conbart/ritterburg/01-Ritterburg-OpenSCAD.png

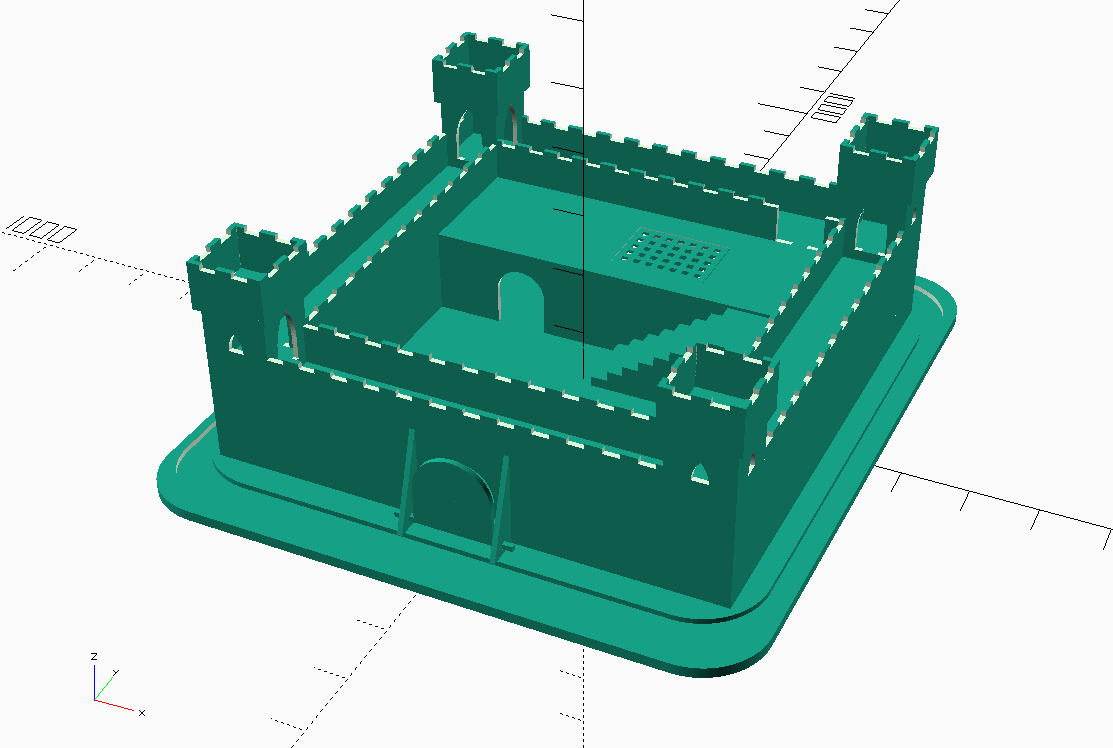
01-Ritterburg-OpenSCAD.png
