conbart/ritterburg/02-Lasercutter-Türme.jpg

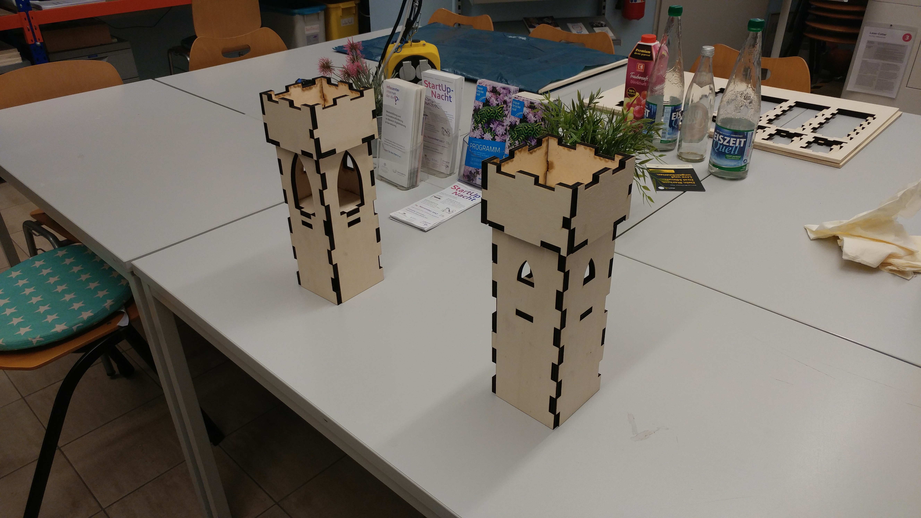
02-Lasercutter-Türme.jpg
