conbart/ritterburg/03-Lasercutter-Burg.jpg

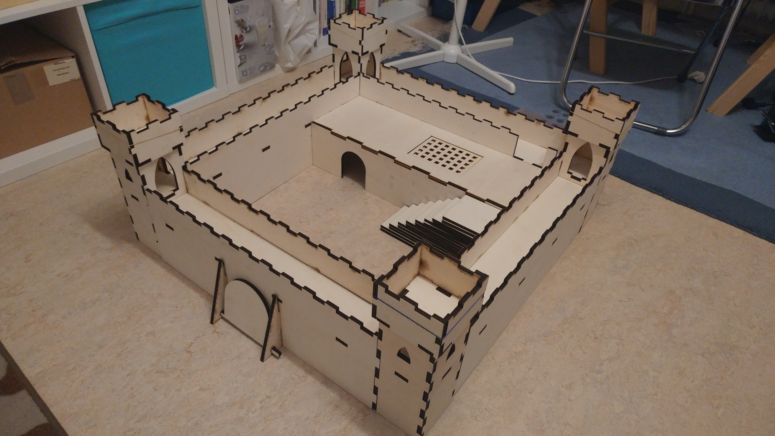
03-Lasercutter-Burg.jpg
