conbart/ritterburg/04-Dremel-Relief.jpg

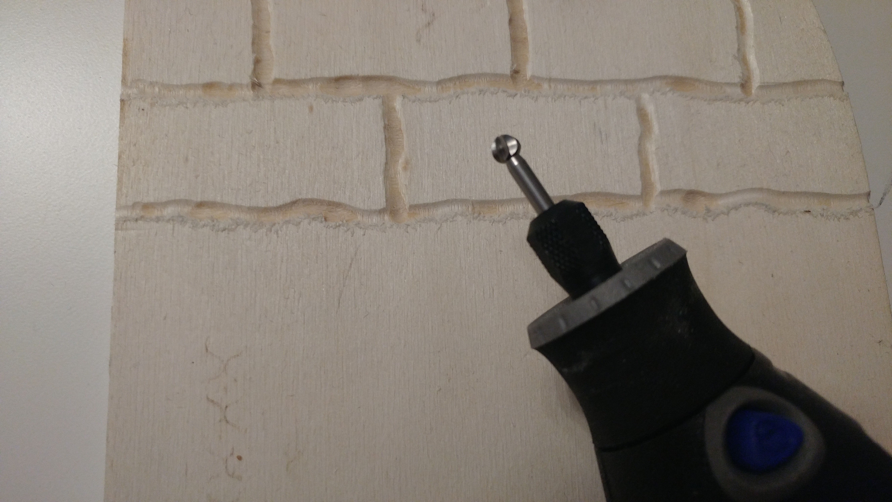
04-Dremel-Relief.jpg
