conbart/ritterburg/05-Turm-Lack.jpg

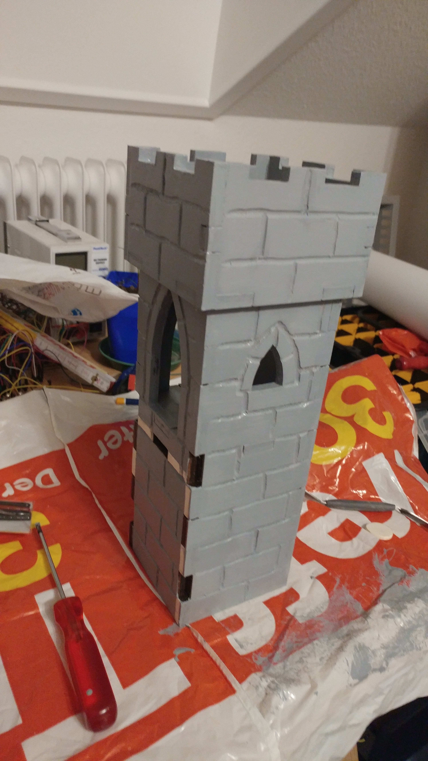
05-Turm-Lack.jpg
