conbart/ritterburg/07-3D-Druck.jpg

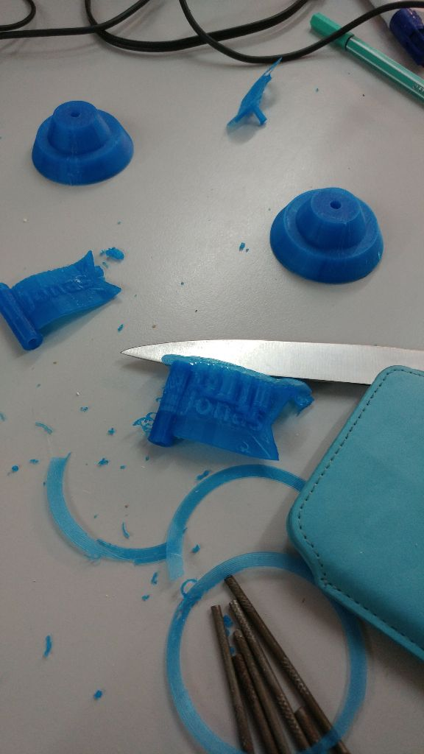
07-3D-Druck.jpg
