conbart/ritterburg/09-Türme.jpg

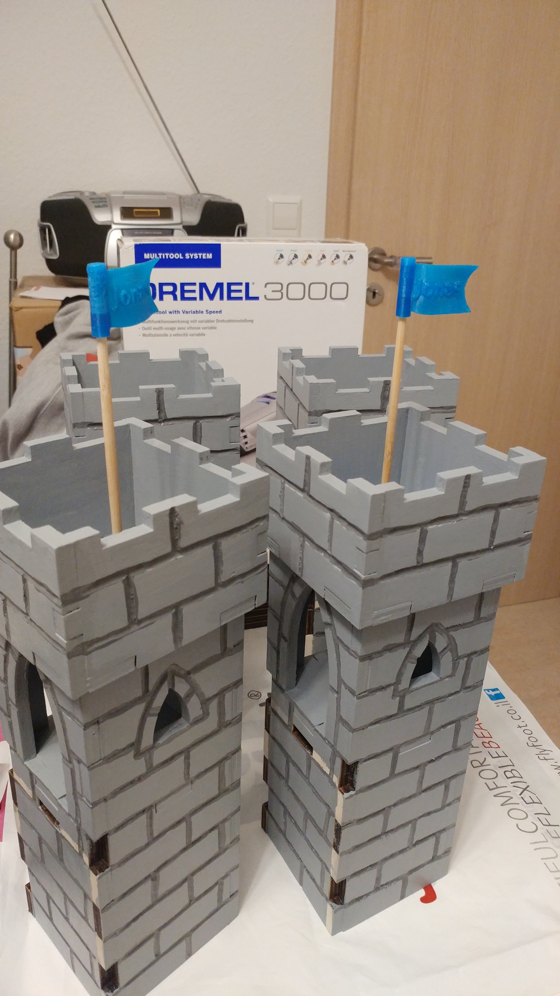
09-Türme.jpg
