conbart/ritterburg/13-Bodenplatte-Wassergraben.jpg

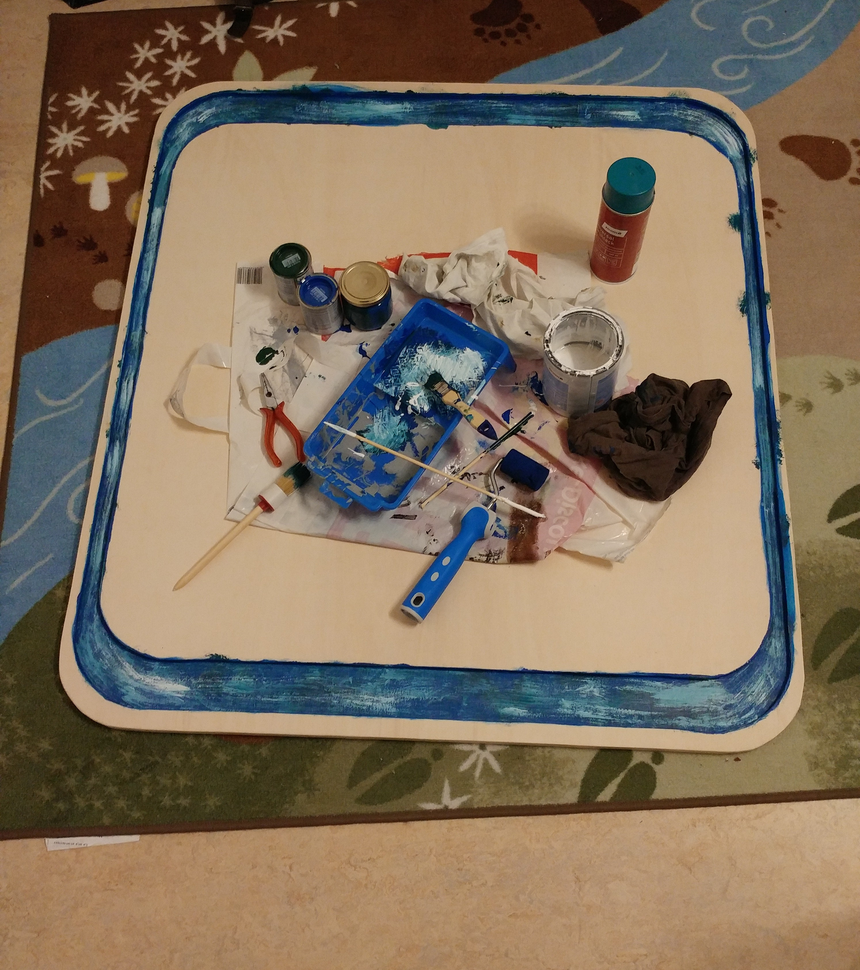
13-Bodenplatte-Wassergraben.jpg
