conbart/ritterburg/14-Ritterburg-mit-unfertiger-Bodenplatte.png

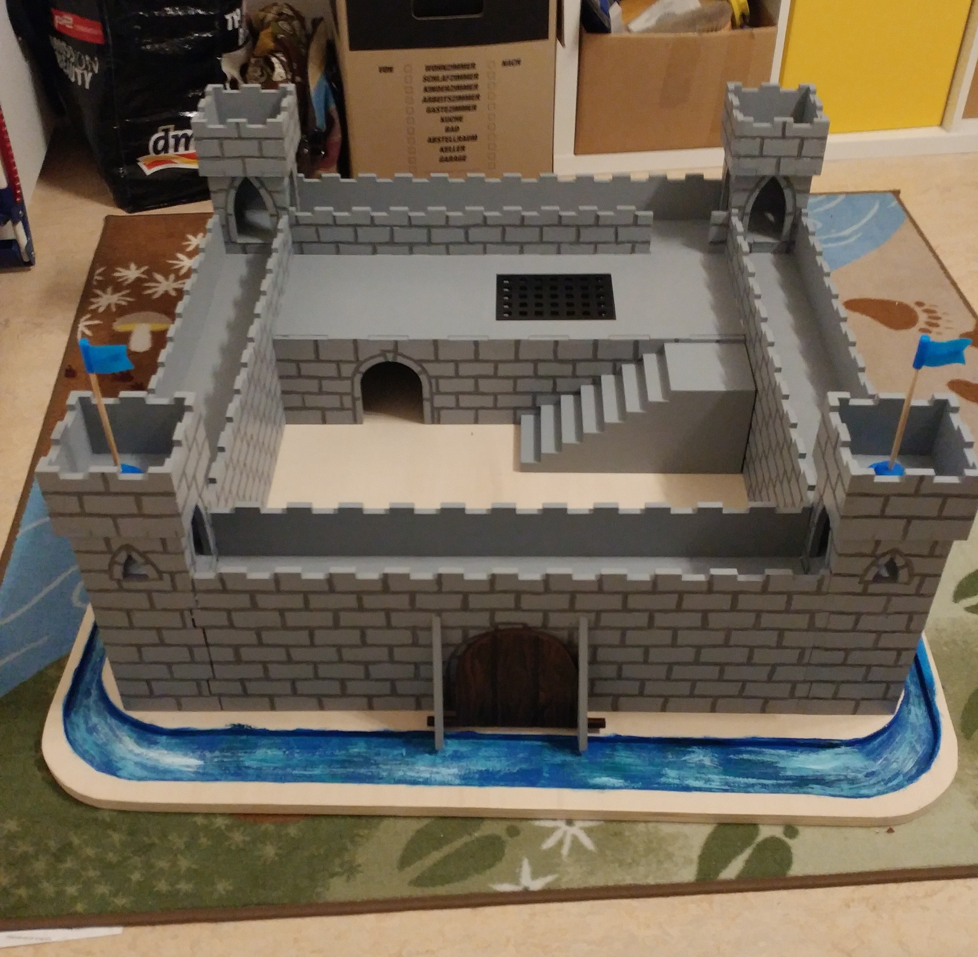
14-Ritterburg-mit-unfertiger-Bodenplatte.png
