conbart/ritterburg/18-Beleuchtung.jpg

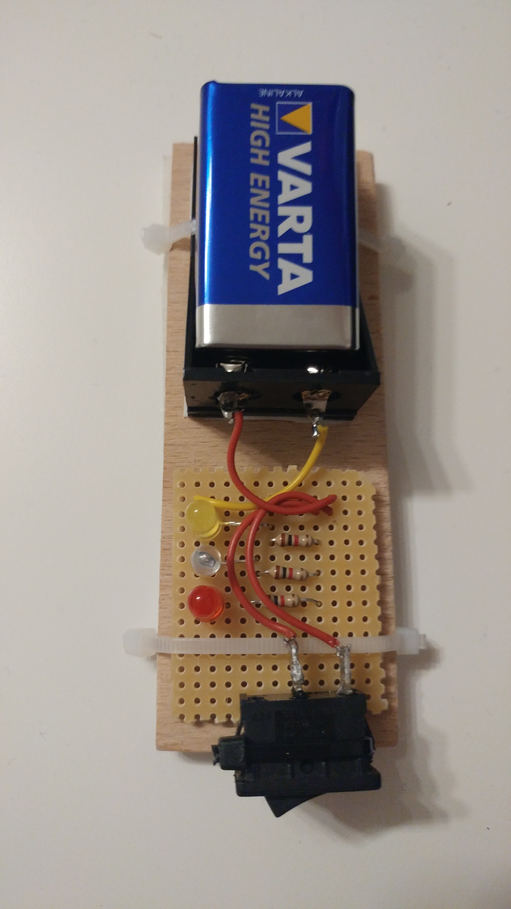
18-Beleuchtung.jpg
