conbart/ritterburg/19-Ritterburg-beleuchtet.jpg

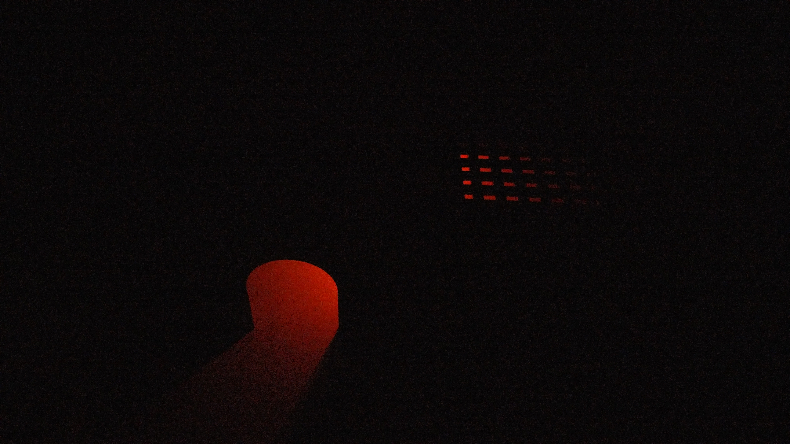
19-Ritterburg-beleuchtet.jpg
